robotlandscape/freetreb/projects/2021 Ganon Cannon/Gallery/20211003_110845.jpg

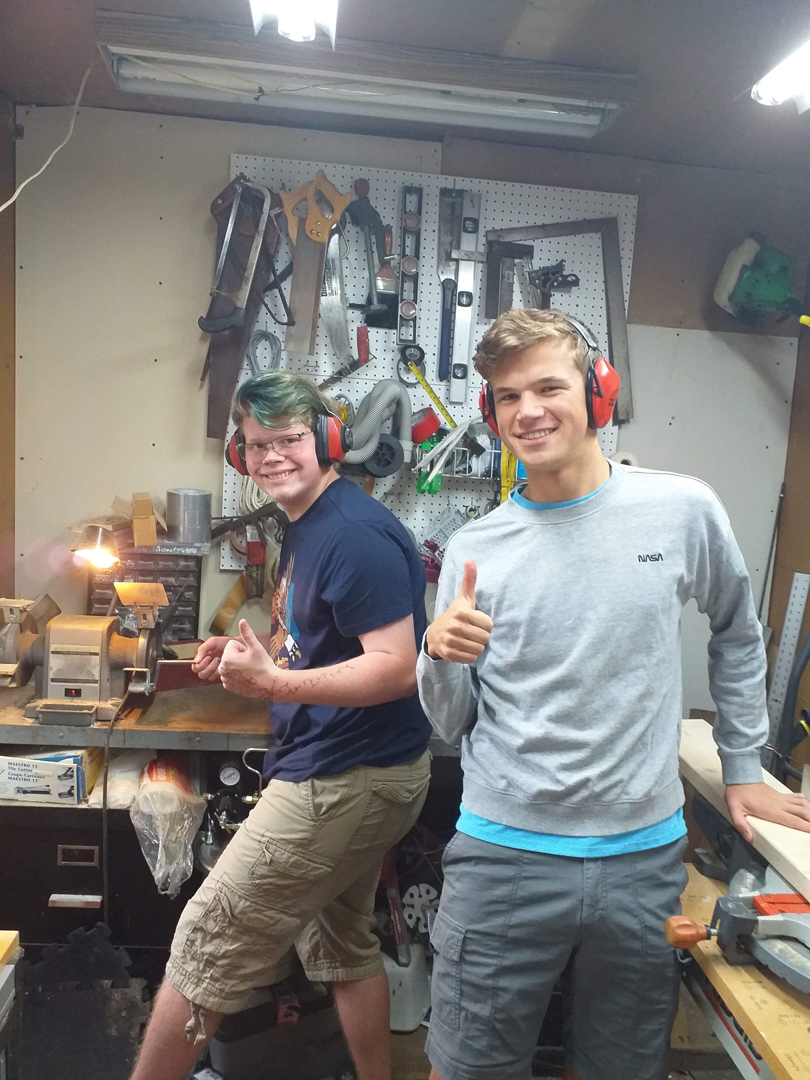
projects/2021 Ganon Cannon/Gallery/20211003_110845.jpg
