robotlandscape/freetreb/projects/2021 Ganon Cannon/Gallery/image1.jpg

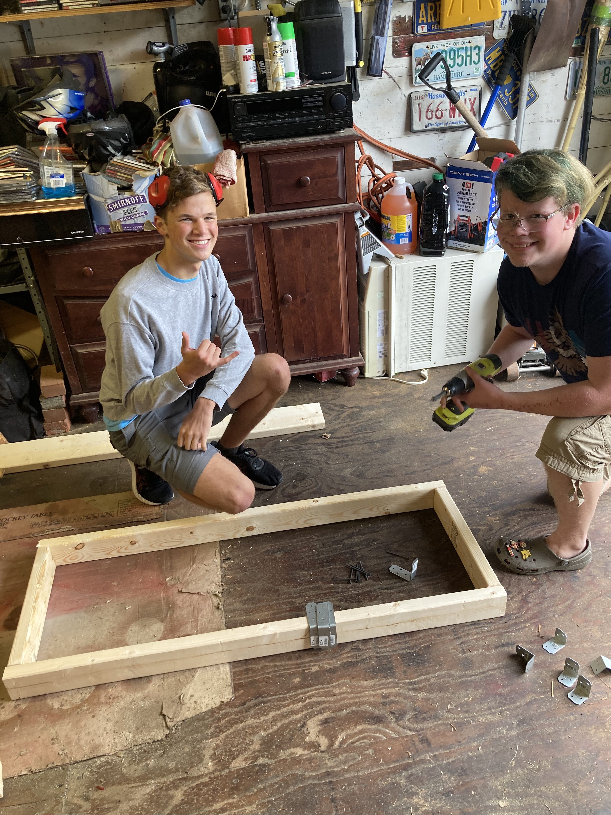
projects/2021 Ganon Cannon/Gallery/image1.jpg
